MOSH-Insa-Toulouse/Amour_Chadi--Amour_Redouane--Lebelguet_Hugo--Benchehida_Yacine--Beyah_Sami--Bouisson_Arnaud/Screen_shots/dimensions.PNG

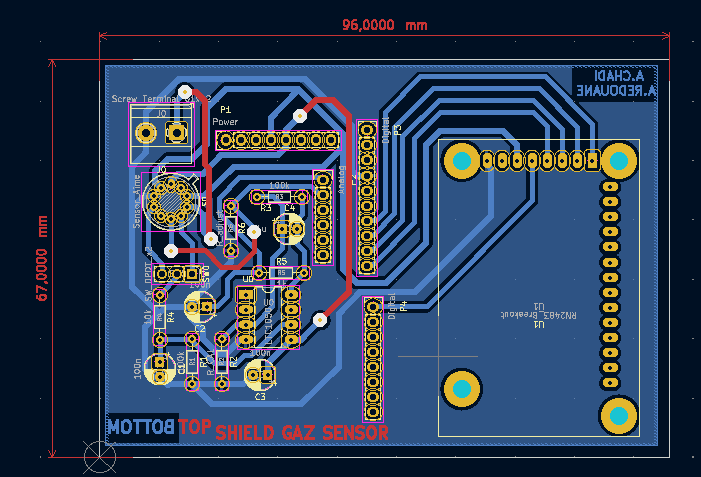
Screen_shots/dimensions.PNG
