MOSH-Insa-Toulouse/Amour_Chadi--Amour_Redouane--Lebelguet_Hugo--Benchehida_Yacine--Beyah_Sami--Bouisson_Arnaud/Screen_shots/Empreintes_schematic/RN2483_BREAKOUT.PNG

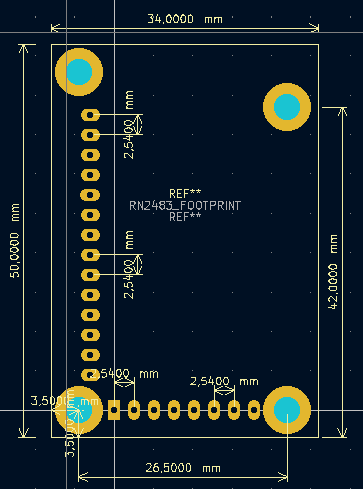
Screen_shots/Empreintes_schematic/RN2483_BREAKOUT.PNG
