MOSH-Insa-Toulouse/Amour_Chadi--Amour_Redouane--Lebelguet_Hugo--Benchehida_Yacine--Beyah_Sami--Bouisson_Arnaud/Screen_shots/PCB_PLAN_DE_MASSE.PNG

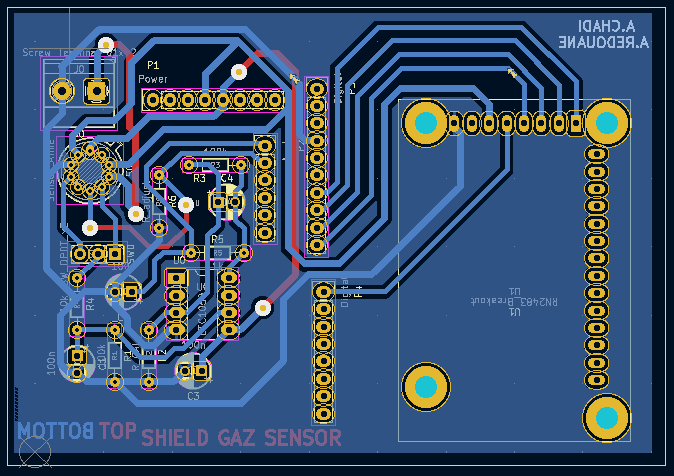
Screen_shots/PCB_PLAN_DE_MASSE.PNG
