MOSH-Insa-Toulouse/Amour_Chadi--Amour_Redouane--Lebelguet_Hugo--Benchehida_Yacine--Beyah_Sami--Bouisson_Arnaud/Screen_shots/schematique_gaz_sensor.PNG

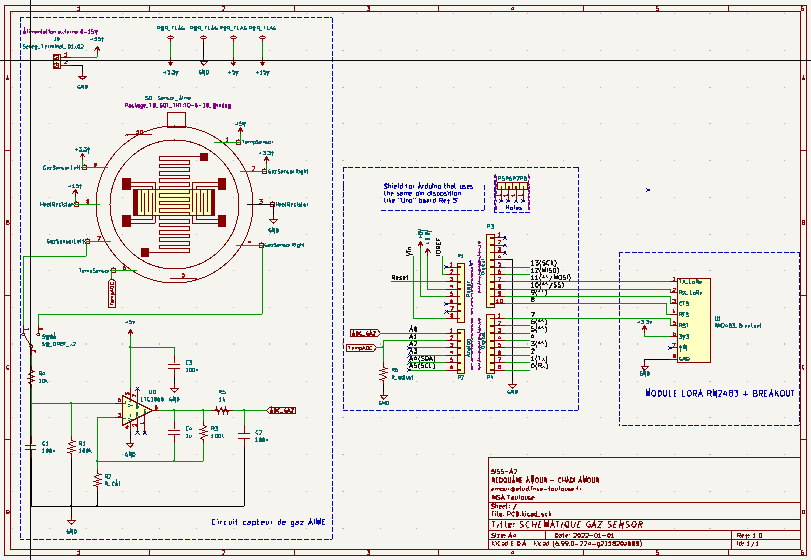
Screen_shots/schematique_gaz_sensor.PNG
