MOSH-Insa-Toulouse/Amour_Chadi--Amour_Redouane--Lebelguet_Hugo--Benchehida_Yacine--Beyah_Sami--Bouisson_Arnaud/Screen_shots/Symboles_schematic/commutateur_a_glissiere_trois_pattes.PNG

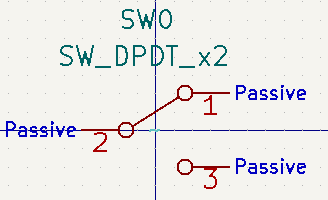
Screen_shots/Symboles_schematic/commutateur_a_glissiere_trois_pattes.PNG
