MOSH-Insa-Toulouse/Amour_Chadi--Amour_Redouane--Lebelguet_Hugo--Benchehida_Yacine--Beyah_Sami--Bouisson_Arnaud/Screen_shots/Symboles_schematic/connecteur_bornier_a_vis.PNG

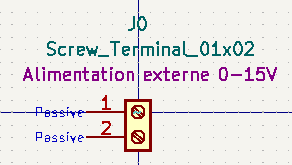
Screen_shots/Symboles_schematic/connecteur_bornier_a_vis.PNG
