MOSH-Insa-Toulouse/Amour_Chadi--Amour_Redouane--Lebelguet_Hugo--Benchehida_Yacine--Beyah_Sami--Bouisson_Arnaud/Screen_shots/Symboles_schematic/sensor_AIME.PNG

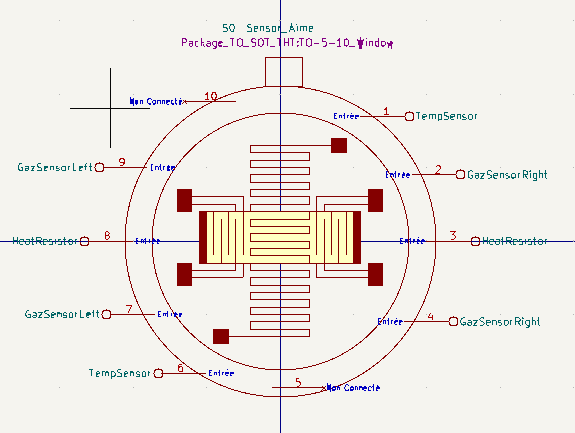
Screen_shots/Symboles_schematic/sensor_AIME.PNG
